diogo-gampe/bms-hardware-prototype/Sim/BMS_Prot_Principal.asc

A1: inv
A2: inv
A3: inv
A4: srflop
A5: inv
A6: srflop
B1: bv; V= idt(V(trip_ocd)/TTRIP, 0, V(trip_ocd) < 0.5)
B2: bv; V=V(V_DRV)
B3: bv; V= idt(V(ntrip_ocd)/TTRIP, 0, V(ntrip_ocd) < 0.5)
B4: bv; V=V(V_DRV)
B5: bv; V= (V(SRP) - V(SRN))
B6: bv; V={ if( (V(CMD_CHG) > 0.5) & V(FAULT_OCC) < 1, 1, 0) }
B7: bv; V={if((V(CMD_DSG) > 0.5) & V(FAULT_OCD) < 1 , 1, 0) }
B8: bv; V= idt(V(trip_occ)/TTRIP, 0, V(trip_occ) < 0.5)
B9: bv; V= idt(V(ntrip_occ)/TTRIP, 0, V(ntrip_occ) < 0.5)
C1: cap; 0.1µ
C2: cap; 0.1µ
C3: cap; 0.1µ
C4: cap; 0.1µ
D1: zener; DI_MMSZ5246B
D2: zener; DI_MMSZ5246B
D3: zener; DI_BAT46W
D4: diode; DI_MMBD914
D5: zener; DI_BAT46W
D6: zener; DI_BAT46W
D7: zener; DI_BAT46W
D8: zener; DI_BAT46W
M1: nmos; IPD200N15N3
M2: nmos; IPD200N15N3
M3: nmos; BSC160N10NS3
R1: res; 5.1k
R2: res; 10Meg
R3: res; 10Meg
R4: res; 5.1k
R5: res; 10k
R6: res; 10k
R8: res; 100k
R9: res; 10Meg
R10: res; 10k
R11: res; 10k
R12: res; 100k
R13: res; 10k
R14: res; 10k
R15: res; 100k
R16: res; 100k
R17: res; 10k
R18: res; 10k
R19: res; 0.4m
R_SHUNT: res; 1m
S1: sw; SW_CHG_EN
S2: sw; SW_DSG_EN
S3: sw; SW_CHG_INV_EN
S4: sw; SW_DSG_INV_EN
S5: sw; SW_CHARGE
S6: sw; SW_LOAD
S7: sw; SWOCD
S8: sw; SWLATCH
S9: sw; SWLATCH
S10: sw; SWOCC
S11: sw; SWLATCH
S12: sw; SWLATCH
V1: voltage; 48
V2: voltage; 11
V3: voltage; PWL(0 1 1.2 1 1.2001 0 2 0)
V4: voltage; PWL(0 0 1.2 0 1.2001 1 2 1)
V6: voltage; 1
V7: voltage; 1
X1: Carregador_Bat; Vdc_charger={V_CHARGER} Vrip_pp={VRIP} f_ripp = {F_RIP} R_out= {ROUT} L_out = {LOUT}
X2: Carga_Bat; MODE = {Load_Type} R_LOAD = {R_Carga} R_ESR_C = {R_Cap_Serie} C_LOAD = {Cap} R_ESR_L = {R_Ind_Serie} L_LOAD = {Ind} V_INIT = {V_Cap_Init}
Named nets: 0, V_DRV, CHG_DRV, DSG_DRV, BAT+, PACK+, CHG, DSG, PACK, LD, PACK-, INV_EN_CHG, INV_EN_DSG, EN_CHG, EN_DSG, D_GATE, C_GATE, TRIP_OCD, nTRIP_OCD, DELAY_OCD, nDELAY_OCD, FAULT_OCD, SRP, SRN, V_CURR, TRIP_OCC, nTRIP_OCC, DELAY_OCC, nDELAY_OCC, FAULT_OCC, CMD_CHG, CMD_DSG
.model SW_CHG_EN SW(Ron=50 Roff=1e9 Vt=0.5 Vh=0)
.model SW_DSG_EN SW(Ron=50 Roff=1e9 Vt=0.5 Vh=0)
.model SW_CHG_INV_EN SW(Ron=1 Roff=1e9 Vt=0.5 Vh=0)
.model SW_DSG_INV_EN SW(Ron=1 Roff=1e9 Vt=0.5 Vh=0)
.model SW_LOAD SW(Ron=1m Roff=1e9 Vt=0.5 Vh=0)
.tran 0 2 1m 50u
Chaveamentos
.model SW_CHARGE SW(Ron=1u Roff=1e9 Vt=0.5 Vh=0)
Tensões DC
Sinais de comando
Sinais de acionamento dos pinos de gate
.model SWOCD SW(Ron=1 Roff=1e9 Vt={VTH} Vh={VH})
.param TTRIP = 20m
.model SWLATCH SW(Ron=1 Roff=1e9 Vt=1 Vh=0)
.param ITRIP=24
.model SWLATCH SW(Ron=1 Roff=1e9 Vt=1 Vh=0)
.model SWOCC SW(Ron=1 Roff=1e9 Vt={VTH} Vh={Vh})
Lógica de detecção de limiar de corrente
.param VTH= 1m*ITRIP
.param VH=0
Temporização da detecção do limiar de corrente em descarga
Temporização da detecção do limiar de corrente em descarga
Tensão sobre o resistor shunt
.param V_CHARGER=50 VRIP=2
.param Load_Type=1
.param R_Carga = 2 R_Cap_Serie = 50m Cap=500m
.param F_RIP = 120 ROUT=50m
.param LOUT=150u
.param R_Ind_Serie = 50m Ind = 500m
.param V_Cap_Init = 0
.lib BAT46W.txt
.lib MMSZ5246B.txt
.lib MMBD914.txt
