diogo-gampe/bms-hardware-prototype/Sim/Carga_Bat.asc

B1: bv; V=if({MODE}==0, 1,0)
B2: bv; V=if({MODE}==1, 1,0)
B3: bv; V=if({MODE}==2, 1,0)
C1: cap; {C_LOAD}; IC={V_INIT}
L1: ind; 1µ
L2: ind; {L_LOAD}
R1: res; 1
R2: res; {R_LOAD}
R3: res; {R_ESR_C}
R4: res; {R_ESR_L}
S1: sw; SW_SELECT
S2: sw; SW_SELECT
S3: sw; SW_SELECT
Named nets: V+, V-, 0, Res_Load, Cap_Load, Ind_Load
.model SW_SELECT SW(Ron=1u Roff=1e9 Vt=0.5 Vh=0)
