diogo-gampe/bms-hardware-prototype/Sim/Carregador_Bat.asc

L1: ind; {L_out}
R1: res; {R_out}
V2: voltage; SINE({Vdc_charger} {Vrip_pp/2} { f_ripp} 0 0 0)
Named nets: V+, V-
